xvrxvr/EventCalendar/spice/sch.asc

C1: cap; 47000µF; V=25 Irms=1
C2: cap; 1nF
D1: schottky; 30BQ060
L1: ind; 40mH; Rser=30
M1: pmos; AO6407
M2: pmos; IRF7406
M3: pmos; IRF7406
Q1: pnp; BC807-40
R1: res; 58
R2: res; 4.6
R3: res; 10K
R4: res; 3.6K
R5: res; 1.8K
R6: res; 5K
U1: TL431
V1: voltage; 15; Rser=0
V2: voltage; PULSE(0 -10 7 0.1 0.1 1000 100000 1)
V3: voltage; 12; Rser=0
Named nets: Vc, On, Sol, 0, R11, R12
.tran 0 15 0 startup uic
