xvrxvr/EventCalendar/soft/firmware/main/common.h

#pragma once

#include <assert.h>
#include <ctype.h>
#include <dirent.h>
#include <errno.h>
#include <inttypes.h>
#include <stdarg.h>
#include <stdint.h>
#include <stdio.h>
#include <stdlib.h>
#include <string.h>
#include <sys/types.h>
#include <time.h>

#include "estring.h"

#include <algorithm>
#include <atomic>
#include <limits>
#include <memory>
#include <optional>
#include <vector>
#include <utility>

// Converts to DOS encode. Returns encoded-size
// Zero terminated encoded buffer if 'length' is -1
int utf8_to_dos(char*, int length=-1);

#include "prnbuf.h"

#include <freertos/FreeRTOS.h>
#include <freertos/semphr.h>
#include <freertos/task.h>
#include <freertos/timers.h>

#include <esp_http_server.h>
#include <esp_log.h>
#include <esp_netif.h>
#include <esp_random.h>
#include <esp_spiffs.h>
#include <esp_system.h>
#include <esp_task_wdt.h>
#include <esp_wifi.h>
#include <mdns.h>
#include <nvs_flash.h>

#include "protocol_examples_utils.h"

#include <driver/gpio.h>
#include <driver/i2c.h>
#include <driver/ledc.h>
#include <driver/spi_master.h>
#include <driver/uart.h>

#include <lwip/apps/netbiosns.h>
#include <lwip/inet.h>

#include <esp_adc/adc_cali_scheme.h>
#include <esp_adc/adc_cali.h>
#include <esp_adc/adc_oneshot.h>

#include <soc/gpio_struct.h>
#include <soc/spi_struct.h>

#pragma GCC diagnostic push
#pragma GCC diagnostic ignored "-Wvolatile"
#include <hal/spi_ll.h>
#pragma GCC diagnostic pop

#define RES_Y 240	//Screen X axis resolution
#define RES_X 400	//Screen Y axis resolution

// Priorities of various tasks
enum TasksPriority {
    TP_Hardware = 5,    // Handling of HW input
    TP_WEBPing  = 1,    // WEB ping task
    TP_LogSender= 5     // Log senter task
};

// task stack sizes
enum TaskStackSize {
    TSS_WEBPing = 8192, // WEB Ping task
    TSS_LogSender = 2048 // Remote Log sender
};

// Generic consts
enum SetupConsts {
    SC_WEBPing_Pings = 2,   // Number of missing Pings to hit threshold
    SC_WEBPing_Time  = 500,  // Time (in MS) between WEB Pings
    SC_HW_INPUT_AUTO_OFF = 1000, // Time (in MS) to automatically passivating HW Input
    SC_TouchTrackInterval = 5, // Time between Touch Track samples (in ticks)
    SC_TouchTrackDeadZone = 5, // Minimal distance in Touch Track to report move
    SC_DebounceTime = 2,    // Debounce time (in ticks)
    SC_TurnoffDelay = 10*60,  // Delay before automatically turn off LCD (in seconds)
    SC_MaxFPScope = 99,     // Maximum FP match scope that not considered as duplication
    SC_FPScope100 = 100,    // What value of Scope equeal to 100% ?
    SC_MaxWS = 16,          // Maximum number of simulteniously opened Websockets
    SC_PingTimeout = 5,     // How much 'ping' signals can we wait for answer
    SC_FileBufSize = 1024,   // Size of buffers for internal file operations
    SC_MAX_CH = 6,          // Maximum number of Characters in FP template
    SC_MinMsgTime = 5000,   // Minimum time to display message (in ms)
    SC_ActivityQueueLength = 16,// Size of Activity Queue. It will holds all pending Actions when no active Activity exists.
    SC_FGEditAnimSpeed = 10, // Animation speed in ticks
    SC_AminPanelTitleGap = 8,// Gap between title line (in Animated panel) and body
    SC_KbMsgShow        = 3, // Time to show message in Keyboard manager (in seconds)
    SC_MultiSelectErr   = 1, // Time to show mesage 'Invalid - try egain" (in seconds)
    SC_LogTaskWKUP      = 100, // Log task forced waikup time (in ms)
    SC_ConnectTout      = 10,  // Timeout for reconnect attempt for Remote Logger (in seconds)
    SC_LogPort          = 5429, // Port of Log server
    SC_LogStartLim      = 1024, // Start memory limit for Remote Log system (to prevent hang on memory overflow on startup)
    SC_CoreFileChunk    = 4096, // Size of chunk of CoreFile when sending them over HTTP
};

#define FINGERPRINT_SENSOR_NORMAL_COLOR ALC_Breathing, ALC_Blue, 1
#define FINGERPRINT_SENSOR_HIDDEN       ALC_Off,       ALC_Red
#define FINGERPRINT_SENSOR_OOB_COLOR    ALC_Breathing, ALC_Red, 1

#define FGEDIT_ICON_COLOR_NOT_FILLED 0xC0,0xC0,0xC0
#define FGEDIT_ICON_COLOR_FILLING_SETUP {               \
    .type = AT_Triange,                                 \
    .color_from = rgb(FGEDIT_ICON_COLOR_NOT_FILLED),    \
    .color_to = 0,                                      \
    .length = 10                                        \
}

#define FGEDIT_ICON_COLOR_FILLED_SETUP {                \
    .type = AT_None,                                    \
    .color_from = 0                                     \
}

#define FGEDIT_ICON_COLOR_ERROR_SETUP {                 \
    .type = AT_Pulse,                                   \
    .color_from = rgb(FGEDIT_ICON_COLOR_NOT_FILLED),    \
    .color_to = rgb(0xFF, 0, 0),                        \
    .length = 20                                        \
}






void reboot(); // Delayed reboot
void send_web_ping_to_ws(const char* tag);

// Detect size of valie UTF8 encoded buffer and returns it. Detect last splitted UTF8 symbol and substruct it from 'length'
int valid_utf8_size(const char*, int length=-1);

struct U {
    char b[4];
};

U dos_to_utf8(char sym);

inline TickType_t s2ticks(uint32_t time) {return time * 1000 / portTICK_PERIOD_MS;}
inline TickType_t ms2ticks(uint32_t time) {return time && time < portTICK_PERIOD_MS ? 1 : time / portTICK_PERIOD_MS;}

// Convert timestamp to ticks
inline TickType_t hit_to_ticks(time_t tm) 
{
    return s2ticks(tm - time(NULL));
}

class Debouncer {
    uint8_t shift_reg = 0;
public:
    bool stable() const {return shift_reg == 0x55 || shift_reg == 0xAA;}    
    bool value() const {return shift_reg == 0x55;}
    void operator <<(bool sw) {shift_reg <<= 2; shift_reg |= sw ? 1 : 2;}
    void clear() {shift_reg = 0;}
};

inline constexpr uint32_t bit(int idx) {return 1 << idx;}

// In file open_doors.cpp
enum OpenDoorResult {
    ODR_Opened      = 0x0100,    // Door was opened. Door index in low 3 bits or FF if door index not known
    ODR_Finished    = 0x0200,    // User exit by 'X' icon
    ODR_Timeout     = 0x0400,    // Exit by timeout
    ODR_Login       = 0x0800,    // New user logged in. User ID in low 5 bit
    ODR_Touch       = 0x1000     // y in low byte, x in high 9 bits
};

// Run interactive GUI for Door open.
// 'door_index' is a door index to open
// Returns bitset of OpenDoorResult (and optionally new user ID in low 5 bits)
uint32_t open_door(int door_index);

// Do upper case (latin & DOS)
uint8_t upcase(uint8_t);

// Read file into 'dst', return true. If file not exists (or read error) - return false
bool read_file(Prn& dst, const char* fname);
