xvrxvr/EventCalendar/soft/firmware/main/hadrware.cpp

#include "common.h"
#include "hadrware.h"

#include "ILI9327_SHIELD.h"
#include "pins.h"
#include "activity.h"

static const char TAG[] = "HW";

#define MY_SPI_HOST    HSPI_HOST

static spi_device_handle_t lcd_spi, sol_spi;
static adc_oneshot_unit_handle_t adc1_handle;

static TaskHandle_t sol_task_handle;

R503 fp_sensor;
LCD lcd;

static const i2c_port_t i2c_master_port = I2C_NUM_0;

#define _RS_COMMAND  gpio_set_level(PIN_NUM_LCD_RS, 0)
#define _RS_DATA gpio_set_level(PIN_NUM_LCD_RS, 1)
#define _LCD_IDLE _RS_DATA

struct CS_EN {
    CS_EN() {gpio_set_level(PIN_NUM_LCD_CS, 0);}
    ~CS_EN() {gpio_set_level(PIN_NUM_LCD_CS, 1); _LCD_IDLE;}
};

struct LCDAccess {
    static int lock_count;
    LCDAccess() {if (!lock_count++) spi_device_acquire_bus(lcd_spi, portMAX_DELAY);}
    ~LCDAccess() {if (!--lock_count) spi_device_release_bus(lcd_spi);}
};

int LCDAccess::lock_count;

#define delay(v) vTaskDelay(ms2ticks(v))

static void sol_task(void*);

inline void LCD::write_lcd(uint8_t d)
{
    spi_transaction_t t{};

    t.length=8;
    t.tx_data[0]=d;
    t.flags = SPI_TRANS_USE_TXDATA;

    ESP_ERROR_CHECK(spi_device_polling_transmit(lcd_spi, &t));
}

#define LCD_HW SPI2

inline void wait4lcd_done() {while(!LCD_HW.slave.trans_done) {;}}
inline void wait4lcd_vacant() {wait4lcd_done(); while (LCD_HW.cmd.val) {;}}


inline void write_lcd_fast(uint8_t data)
{
    LCD_HW.slave.trans_done = 0;
    LCD_HW.data_buf[0] = data;
    LCD_HW.cmd.usr = 1;
    wait4lcd_done();

    GPIO.out_w1tc = 1 << PIN_NUM_LCD_WR;
    GPIO.out_w1ts = 1 << PIN_NUM_LCD_WR;
}

inline void LCD::_WRITE_DATA(uint8_t d)
{
    write_lcd(d);
    gpio_set_level(PIN_NUM_LCD_WR, 0);
    gpio_set_level(PIN_NUM_LCD_WR, 1);
}

inline void _WRITE_DATA_FAST(uint8_t d)
{
    write_lcd_fast(d);
}

inline void write_sol(uint8_t data)
{
    spi_transaction_t t{};

    t.length=8;
    t.tx_data[0]=data;
    t.flags = SPI_TRANS_USE_TXDATA;

    ESP_ERROR_CHECK(spi_device_polling_transmit(sol_spi, &t));
}


/* Internal function writes an 8 bit command byte to the display */
inline void LCD::_WriteCommand(uint8_t command)
{
	_RS_COMMAND;
	_WRITE_DATA(command);
}



/* Internal function writes an 8 bit data parameter byte to the display */
inline void _WriteData(uint8_t data)
{
	_RS_DATA;
	_WRITE_DATA_FAST(data);
}


/* Resets the interface */
void LCD::DReset(void)
{
	CS_EN cs_en;
	
	_WriteCommand(REG_RESET); //Soft reset
    delay(200);
}

// Writes the initial setting to the screen. Settings are taken from the ILI9325 application note.
void LCD::init_screen(void)
{
	DReset();	

    LCDAccess lcd_access;
    CS_EN cs_en;
	
	_WriteCommand(REG_DISPOFF);
	_WriteCommand(REG_EXITSLEEP);
	delay(120); //Must wait 120ms after exiting sleep 
	_WriteCommand(REG_CMDPROTECT);
	_WriteData(0x00);
	_WriteCommand(REG_DISPTIMING);
	_WriteData(0x10);
	_WriteData(0x10);
	_WriteData(0x02);
	_WriteData(0x02);
	_WriteCommand(REG_PANELDRIVE);
	_WriteData(0x00);
	_WriteData(0x35);
	_WriteData(0x00);
	_WriteData(0x00);
	_WriteData(0x01);
	_WriteData(0x02);
	_WriteCommand(REG_FRAMERATE);
	_WriteData(0x04);
	_WriteCommand(REG_PWRNORMMODE);
	_WriteData(0x01);
	_WriteData(0x04);
	_WriteCommand(REG_3GAMMA);
	_WriteData(0x80);
//	_WriteCommand(REG_ADDRMODE);
//	_WriteData(0x48);
	_WriteCommand(REG_PIXELFORMAT);
	_WriteData(0x55);
	_WriteCommand(REG_COLADDR);
	_WriteData(0x00);
	_WriteData(0x00);
	_WriteData(0x00);
	_WriteData(0xEF);
	_WriteCommand(REG_PAGEADDR);
	_WriteData(0x00);
	_WriteData(0x00);
	_WriteData(0x01);
	_WriteData(0x8F);
	_WriteCommand(REG_PARAREA);
	_WriteData(0x00);
	_WriteData(0x00);
	_WriteData(0x01);
	_WriteData(0x8F);
	_WriteCommand(REG_DISPON);
}

/* Places the screen in to or out of sleep mode where:
	mode is the required state. Valid values area
		true (screen will enter sleep state)
		false (screen will wake from sleep state)
*/
void LCD::DSleep(bool mode)
{
    {
        CS_EN cs_en;
    	
    	if(mode)
    	{
    		_WriteCommand(REG_ENTERSLEEP);
    	}
    	else
    	{
    		_WriteCommand(REG_EXITSLEEP);
    	}
    }
	delay(120);
} 
	



/* Turn the screen on or off where:
	mode is the required state. Valid values are
		ON (screen on)
		OFF (screen off)
*/
void LCD::DScreen(bool mode)
{
    CS_EN cs_en;
	
	if(mode)
		_WriteCommand(REG_DISPON);	//Screen on
	else
		_WriteCommand(REG_DISPOFF);  //Screen off
}




/* Sets the screen orientation and write direction where:
	mode is the direction, orientation to set the screen to. Valid vales are:
		SCREEN_NORMAL 		(Default)
		SCREEN_R90 			Screen is rotated 90o		
		SCREEN_R180 		Screen is rotated 180o
		SCREEN_R270 		Screen is rotated 270o		
*/
void LCD::DFlip(uint8_t mode)
{
	_FlipMode = mode;
	_res_x = RES_Y;
	_res_y = RES_X;
    CS_EN cs_en;
	switch(mode)
	{
		case(SCREEN_NORMAL): LCD_CtrlWrite_ILI9327(REG_ADDRMODE, 0b00001000); return;
		case(SCREEN_R90):	 LCD_CtrlWrite_ILI9327(REG_ADDRMODE, 0b10101000); break;
		case(SCREEN_R180):	 LCD_CtrlWrite_ILI9327(REG_ADDRMODE, 0b11001000); return;
		case(SCREEN_R270):	 LCD_CtrlWrite_ILI9327(REG_ADDRMODE, 0b00101000); break;	
	}
   	_res_x = RES_X;
   	_res_y = RES_Y;
}

/* Draws a solid rectangle to the using the current foreground colour where:
	x1 is the x coordinate of the top left corner of the rectangle.
	y1 is the y coordinate of the top left corner of the rectangle.
	x2 is the x coordinate of the bottom right corner of the rectangle.
	y2 is the y coordinate of the bottom right corner of the rectangle.
*/
void LCD::DRect(int16_t x1, int16_t y1, int16_t x2, int16_t y2, uint16_t color)
{
    LCDAccess lcd;
    CS_EN cs_en;
    
    _SetWriteArea(x1, y1, x2, y2);
    _WriteCommand(REG_WRITEMEM); //Write to RAM

    uint32_t total = (x2-x1+1)*(y2-y1+1);
    uint8_t col_high = color >> 8;
    uint8_t col_low = color & 0xFF;
    while(total--)
    {
        _WriteData(col_high); 
        _WriteData(col_low); 
    }
    wait4lcd_vacant();
}

// Draw buffer in format RGB888
void LCD::draw_rgb888(int16_t x1, int16_t y1, int16_t x2, int16_t y2, uint8_t* data)
{
    LCDAccess lcd;
    CS_EN cs_en;

    _SetWriteArea(x1, y1, x2, y2);
    _WriteCommand(REG_WRITEMEM); //Write to RAM

    for(int yy = y1; yy <= y2; ++yy)
    {
        for(int xx = x1; xx <= x2; ++xx, data += 3)
        {
            // |RRRRR:GGG|GGG:BBBBB|
            uint8_t color_high = (data[0] & 0xF8) | ((data[1] >> 5) & 7);
            uint8_t color_low = ((data[2] >> 3) & 0x1F) | ((data[1] << 3 ) & 0xE0);
            _WriteData(color_high); 
            _WriteData(color_low); 
        }
    }
    wait4lcd_vacant();
}

void LCD::WImgPallete(int16_t x1, int16_t y1, int16_t w, int16_t h, const uint8_t* image, const uint16_t* pallete, bool with_clip)
{
    if (with_clip) {WImgPalleteClip(x1, y1, w, h, image, pallete); return;}
    LCDAccess lcd;
    CS_EN cs_en;

    int16_t x2 = x1 + w - 1;
    int16_t y2 = y1 + h - 1;

    _SetWriteArea(x1, y1, x2, y2);
    _WriteCommand(REG_WRITEMEM); //Write to RAM
    for(int yy = y1; yy <= y2; ++yy)
    {
        for(int xx = x1; xx <= x2; ++xx, ++image)
        {
            uint16_t color = pallete[*image];
            _WriteData(uint8_t(color >> 8)); 
            _WriteData(uint8_t(color)); 
        }
    }
    wait4lcd_vacant();
}

void LCD::WImgPalleteClip(int16_t x1, int16_t y1, int16_t w, int16_t h, const uint8_t* image, const uint16_t* pallete)
{
    const uint8_t* row_end = image + w - 1;
    const uint8_t* start = image;
    int16_t start_row = 0;
    int16_t row = 0;

    auto flush = [&, this]()
    {
        if (row > start_row && start_row < h)
        {
            WImgPallete(x1, y1+start_row, w, row - start_row, start, pallete);
            start_row = row;
            start = image;
        }
    };

    for(; row < h; ++row, image += w, row_end += w)
    {
        if (*image == 0 || *row_end == 0)
        {
            flush();
            const uint8_t* b = image;
            const uint8_t* e = row_end+1;
            while(*b == 0 && b < e) ++b;
            while(e[-1] == 0 && b < e) --e;
            if (b != e) WImgPallete(x1 + (b-image), y1+row, e-b, 1, b, pallete);
            start = image + w;
            start_row = row+1;
        }
    }
    flush();
}

#define RNG(var, limit) if (var < 0) var = 0; else if (var >= limit) var = limit-1
void LCD::_SetWriteAreaDelta(int16_t& X1, int16_t& Y1, int16_t dx, int16_t dy)
{
    RNG(X1, _res_x);
    RNG(Y1, _res_y);
    int16_t X2 = X1 + dx - 1;
    int16_t Y2 = Y1 + dy - 1;
    _SetWriteArea(X1, Y1, X2, Y2);
}

void LCD::_SetWriteArea(int16_t& X1, int16_t& Y1, int16_t& X2, int16_t& Y2)
{
	//Make sure none of the area to write to is outside the display area. If so then crop it
    RNG(X1, _res_x);
    RNG(X2, _res_x);
    RNG(Y1, _res_y);
    RNG(Y2, _res_y);
#undef RNG
    if (X1 > X2) std::swap(X1, X2);
    if (Y1 > Y2) std::swap(Y1, Y2);

    uint16_t x1 = X1, x2 = X2, y1 = Y1, y2= Y2;

	//Adjust screen offset depending or orientation
	switch(_FlipMode)
	{
		case(SCREEN_NORMAL): break;
		case(SCREEN_R270): std::swap(x1, y1); std::swap(x2, y2); break;
			
		case(SCREEN_R90): std::swap(x1, y1); std::swap(x2, y2); break;
//			y1 += 32;
//			y2 += 32;
			break;
			
		case(SCREEN_R180):
//			x1 += 32;
//			x2 += 32;
			break;
	}
    LCDAccess lcd_access;
	
	//Set the memory write window
	_WriteCommand(REG_COLADDR);
	_WriteData(y1>>8);
	_WriteData(y1);
	_WriteData(y2>>8);
	_WriteData(y2);
	_WriteCommand(REG_PAGEADDR);
	_WriteData(x1>>8);
	_WriteData(x1);
	_WriteData(x2>>8);
	_WriteData(x2);
}



/* Internal function that writes 16 bits of data to one of the displays registers */
void LCD::LCD_CtrlWrite_ILI9327(uint8_t command, uint8_t data)
{
    LCDAccess lcd_access;
	_WriteCommand(command);
	_WriteData(data);
}

static const uint8_t font[] = {
    0x00,0x00,0x00,0x00,0x00,0x00,0x00,0x00,0x00,0x00,0x00,0x00,0x00,0x00,0x00,0x00,

// Symbol BS:   1, 2    (Len 2 - 1,2)
    0x00, 0x00, 0x07, 0x0F, 0x18, 0x33, 0x61, 0xC0, 0x61, 0x33, 0x18, 0x0F, 0x07, 0x00, 0x00, 0x00,
    0x00, 0x00, 0xFE, 0xFE, 0x06, 0x36, 0xE6, 0xC6, 0xE6, 0x36, 0x06, 0xFE, 0xFE, 0x00, 0x00, 0x00,
// Symbol ENT:  3, 4, 5 (Len 2 - 3, 4; Len 3 - 3,5,4)
    0x00, 0x00, 0x00, 0x0C, 0x18, 0x30, 0x60, 0xFF, 0xFF, 0x60, 0x30, 0x18, 0x0C, 0x00, 0x00, 0x00,
    0x00, 0x00, 0x00, 0x00, 0x00, 0x06, 0x06, 0xFE, 0xFE, 0x00, 0x00, 0x00, 0x00, 0x00, 0x00, 0x00,
    0x00, 0x00, 0x00, 0x00, 0x00, 0x00, 0x00, 0xFF, 0xFF, 0x00, 0x00, 0x00, 0x00, 0x00, 0x00, 0x00,
// Symbol SP:   6, 7, 8  (Len 2: 6,7, Len 3... - 6, 8..., 7)
    0x00, 0x00, 0x00, 0x00, 0x00, 0x00, 0x00, 0x00, 0x60, 0x60, 0x7F, 0x7F, 0x00, 0x00, 0x00, 0x00,
    0x00, 0x00, 0x00, 0x00, 0x00, 0x00, 0x00, 0x00, 0x06, 0x06, 0xFE, 0xFE, 0x00, 0x00, 0x00, 0x00,
    0x00, 0x00, 0x00, 0x00, 0x00, 0x00, 0x00, 0x00, 0x00, 0x00, 0xFF, 0xFF, 0x00, 0x00, 0x00, 0x00,
// Symbol Lang:  9
    0x00, 0x00, 0x00, 0x3C, 0x5A, 0xA5, 0xFF, 0xA5, 0xFF, 0xA5, 0x5A, 0x3C, 0x00, 0x00, 0x00, 0x00,

//    0x00,0x00,0x7e,0x81,0xa5,0x81,0x81,0xbd,0x99,0x81,0x81,0x7e,0x00,0x00,0x00,0x00,
//    0x00,0x00,0x7e,0xff,0xdb,0xff,0xff,0xc3,0xe7,0xff,0xff,0x7e,0x00,0x00,0x00,0x00,
//    0x00,0x00,0x00,0x00,0x6c,0xfe,0xfe,0xfe,0xfe,0x7c,0x38,0x10,0x00,0x00,0x00,0x00,
//    0x00,0x00,0x00,0x00,0x10,0x38,0x7c,0xfe,0x7c,0x38,0x10,0x00,0x00,0x00,0x00,0x00,
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
{
    LCDAccess lcd;
    CS_EN cs_en;

    const uint8_t fc_high = uint8_t(color >> 8);
    const uint8_t fc_low = uint8_t(color);
    
    _SetWriteAreaDelta(x, y, 32, 32);
    _WriteCommand(REG_WRITEMEM); //Write to RAM

    for(int dy=0; dy<32; ++dy, ++y)
    {
        uint32_t bits = *icon++;
        uint8_t cnt=32;
        do {
            if (bits&0x80000000) {_WriteData(fc_high); _WriteData(fc_low);}
            else {_WriteData(bc_high); _WriteData(bc_low);}
            bits <<= 1;
        } while (--cnt);
    }
    wait4lcd_vacant();
}

void LCD::text2(const char* text, int16_t x, int16_t y, int txt_len)
{
    LCDAccess lcd;
    CS_EN cs_en;

    if (txt_len == -1) txt_len = strlen(text);
    if (x == -1) x = midx(txt_len*2);
    _SetWriteAreaDelta(x, y, txt_len<<4, 32);
    _WriteCommand(REG_WRITEMEM); //Write to RAM

    for(uint8_t scan_line=0; scan_line!=32; ++scan_line)
    {
        int tl = txt_len;
        for(const char* t=text;tl--; ++t)
        {
            uint8_t sym = *t;
            uint8_t bits = font[sym*16+(scan_line>>1)];
            uint8_t cnt=8;
            do {
                if (bits&0x80) {_WriteData(fc_high); _WriteData(fc_low); _WriteData(fc_high); _WriteData(fc_low);}
                else {_WriteData(bc_high); _WriteData(bc_low); _WriteData(bc_high); _WriteData(bc_low);}
                bits <<= 1;
            } while (--cnt);
        }
    }
    wait4lcd_vacant();
}

#undef _B
#define _B(n) (1ull<<(n))

void hw_init()
{
    gpio_set_level(PIN_NUM_OE_SOL, 1);
    gpio_set_level(PIN_NUM_LCD_CS, 1);
    gpio_set_level(PIN_NUM_LCD_SW1, 1);
    gpio_set_level(PIN_NUM_LCD_SW2, 1);
    gpio_set_level(PIN_NUM_LCD_WR, 1);
    gpio_set_level(PIN_NUM_LCD_BL, 1);

    gpio_config_t gpio_cfg_out = {
        .pin_bit_mask = _B(PIN_NUM_OE_SOL)|_B(PIN_NUM_LCD_CS)|_B(PIN_NUM_LCD_BL)|_B(PIN_NUM_LCD_SW1)|_B(PIN_NUM_LCD_SW2)|_B(PIN_NUM_LCD_WR)|_B(PIN_NUM_LCD_RS),
        .mode = GPIO_MODE_OUTPUT,
        .pull_up_en = GPIO_PULLUP_DISABLE,
        .pull_down_en = GPIO_PULLDOWN_DISABLE,
        .intr_type = GPIO_INTR_DISABLE
    };
    ESP_ERROR_CHECK(gpio_config(&gpio_cfg_out));
    gpio_config_t gpio_cfg_in = {
        .pin_bit_mask = _B(PIN_NUM_FP_WAKEUP)|_B(PIN_NUM_DIPSW_BOOT)|_B(PIN_NUM_DIPSW_AUX),
        .mode = GPIO_MODE_INPUT,
        .pull_up_en = GPIO_PULLUP_ENABLE,
        .pull_down_en = GPIO_PULLDOWN_DISABLE,
        .intr_type = GPIO_INTR_DISABLE
    };
    ESP_ERROR_CHECK(gpio_config(&gpio_cfg_in));

    gpio_set_level(PIN_NUM_OE_SOL, 1);
    gpio_set_level(PIN_NUM_LCD_CS, 1);
    gpio_set_level(PIN_NUM_LCD_SW1, 1);
    gpio_set_level(PIN_NUM_LCD_SW2, 1);
    gpio_set_level(PIN_NUM_LCD_WR, 1);
    gpio_set_level(PIN_NUM_LCD_BL, 1);

    gpio_set_intr_type(PIN_NUM_FP_WAKEUP, GPIO_INTR_NEGEDGE);
    gpio_set_intr_type(PIN_NUM_LCD_RS, GPIO_INTR_ANYEDGE); // This is Touch sence pin

    spi_bus_config_t buscfg={
        .mosi_io_num=PIN_NUM_MOSI,
        .miso_io_num=-1,
        .sclk_io_num=PIN_NUM_CLK,
        .quadwp_io_num=-1,
        .quadhd_io_num=-1,
        .max_transfer_sz=10
    };
    spi_device_interface_config_t lcd_devcfg={
        .mode=0,
        .clock_speed_hz=SPI_MASTER_FREQ_80M,
        .spics_io_num=PIN_NUM_CS_LCD,
        .flags = SPI_DEVICE_NO_DUMMY,
        .queue_size=1
    };
    spi_device_interface_config_t sol_devcfg={
        .mode=0,
        .clock_speed_hz=SPI_MASTER_FREQ_10M,
        .spics_io_num=PIN_NUM_CS_SOL,
        .queue_size=1
    };
    //Initialize the SPI bus
    ESP_ERROR_CHECK(spi_bus_initialize(MY_SPI_HOST, &buscfg, SPI_DMA_CH_AUTO));

    //Attach the LCD to the SPI bus
    ESP_ERROR_CHECK(spi_bus_add_device(MY_SPI_HOST, &lcd_devcfg, &lcd_spi));

    //Attach the Solenoids to the SPI bus
    ESP_ERROR_CHECK(spi_bus_add_device(MY_SPI_HOST, &sol_devcfg, &sol_spi));

    // Zero Solenoid register, then OE it
    write_sol(0);
    gpio_set_level(PIN_NUM_OE_SOL, 0);

    // ADC config
    adc_oneshot_unit_init_cfg_t init_config1 = {
        .unit_id = ADC_UNIT_1,
    };
    ESP_ERROR_CHECK(adc_oneshot_new_unit(&init_config1, &adc1_handle));

    adc_oneshot_chan_cfg_t config = {
        .atten = ADC_ATTEN_DB_11,
        .bitwidth = ADC_BITWIDTH_DEFAULT,
    };
    ESP_ERROR_CHECK(adc_oneshot_config_channel(adc1_handle, ADC_Y_PLUS, &config));
    ESP_ERROR_CHECK(adc_oneshot_config_channel(adc1_handle, ADC_X_MINUS, &config));

    // LCD
    delay(50);
    {
	    lcd.init_screen();
    	lcd.DFlip(LCD::SCREEN_MY);
    	lcd.DRect(0, 0, LCD::MAX, LCD::MAX, 0);
    }

    // Configure I2C
    i2c_port_t i2c_master_port = I2C_NUM_0;
    i2c_config_t conf = {
        .mode = I2C_MODE_MASTER,
        .sda_io_num = PIN_NUM_I2C_SDA,
        .scl_io_num = PIN_NUM_I2C_SCL,
        .sda_pullup_en = GPIO_PULLUP_DISABLE,
        .scl_pullup_en = GPIO_PULLUP_DISABLE,
        .master = {
            .clk_speed = 100'000
        }
    };

    i2c_param_config(i2c_master_port, &conf);

    ESP_ERROR_CHECK(i2c_driver_install(i2c_master_port, conf.mode, 0, 0, 0));

    ESP_ERROR_CHECK(ledc_fade_func_install(ESP_INTR_FLAG_LEVEL1));

    ledc_timer_config_t ledc_timer = {
        .speed_mode       = LEDC_HIGH_SPEED_MODE,
        .duty_resolution  = LEDC_TIMER_13_BIT,
        .timer_num        = LEDC_TIMER_0,
        .freq_hz          = 5000,  // Set output frequency at 5 kHz
        .clk_cfg          = LEDC_AUTO_CLK
    };
    ESP_ERROR_CHECK(ledc_timer_config(&ledc_timer));

    // Prepare and then apply the LEDC PWM channel configuration
    ledc_channel_config_t ledc_channel = {
        .gpio_num       = PIN_NUM_LCD_BL,
        .speed_mode     = LEDC_HIGH_SPEED_MODE,
        .channel        = LEDC_CHANNEL_0,
        .intr_type      = LEDC_INTR_DISABLE,
        .timer_sel      = LEDC_TIMER_0,
        .duty           = (1<<13)-1,
        .hpoint         = 0
    };
    ESP_ERROR_CHECK(ledc_channel_config(&ledc_channel));

    const uart_port_t uart_num = UART_NUM_2;
    uart_config_t uart_config = {
        .baud_rate = 57600,
        .data_bits = UART_DATA_8_BITS,
        .parity = UART_PARITY_DISABLE,
        .stop_bits = UART_STOP_BITS_1,
        .flow_ctrl = UART_HW_FLOWCTRL_DISABLE,
        .rx_flow_ctrl_thresh = 0,
        .source_clk = UART_SCLK_DEFAULT
    };
    // Configure UART parameters
    ESP_ERROR_CHECK(uart_param_config(uart_num, &uart_config));
    ESP_ERROR_CHECK(uart_set_pin(UART_NUM_2, PIN_NUM_FP_RXD, PIN_NUM_FP_TXD, -1, -1));

    ESP_ERROR_CHECK(uart_driver_install(UART_NUM_2, 2048, 0, 0, NULL, 0));

    xTaskCreate(sol_task, "Sol", 2048, NULL, tskIDLE_PRIORITY+1, &sol_task_handle);

    delay(150);
    auto err = fp_sensor.init();
    
    if (err != R503_SUCCESS)
    {
        printf("FP_sensor init error: %s\n", R503::errorMsg(err));
        abort();
    }
    fp_sensor.setAuraLED(auraOff);
}
#undef _B


void sol_hit(int index)
{
    xTaskNotify(sol_task_handle, (index&7)+1, eSetValueWithOverwrite);
    ESP_LOGI(TAG, "Sol: Signal %d", index);
}

/*
    BL      - 5           LCD    TouchX TouchXInv TouchY  TouchYInv  TouchSence     TouchSence/Alt    Idle
    DB7/Y- (SW1) - 27    1/DB7     0      0         1/0     1/1          1/0             0             1/1
    DB6/X+ (SW2) - 26    1/DB6    1/1    1/0         0       0            0             1/0            1/1
    WR/Y+   - 21          WR      ADC    ADC         1       0            0           PullUP/Sence      1       -> 36 (SENSOR_VP)
    RS/X-   - 19          RS       0      1         ADC     ADC        PullUP/Sence      0              1       -> 39 (SENSOR_VN)
*/

enum TTSetup {
    TTS_SW1     = 0x01,
    TTS_SW2     = 0x02,
    TTS_WR_ADC  = 0x04,
    TTS_WR      = 0x08,
    TTS_RS_ADC  = 0x10,
    TTS_RS      = 0x20,
    TTS_DB6     = 0x40,   // Do not change value!
    TTS_DB7     = 0x80,   // Do not change value!
    TTS_RS_SNS  = 0x100
};

static const int tts_setup [] = {
    TTS_SW1 | TTS_SW2 | TTS_WR | TTS_RS,         // TT_LCD
    TTS_SW2 | TTS_DB6 | TTS_WR_ADC,              // TT_X
    TTS_SW2 | TTS_WR_ADC | TTS_RS,               // TT_XInv
    TTS_SW1 | TTS_WR | TTS_RS_ADC,               // TT_Y
    TTS_SW1 | TTS_DB7 | TTS_RS_ADC,              // TT_YInv
    TTS_SW1 | TTS_RS_SNS                         // TT_Sence
};

#define NOP() __asm volatile("nop")

static const int adc_reads = 255;

int touch_config(TouchType tt)
{
    int read_adc = -1;
    int setup = tts_setup[tt];
#define V(name) ((setup & TTS_##name) != 0)
    wait4lcd_vacant();
    lcd.write_lcd(setup & 0xC0); // DB6 & DB7
    gpio_set_level(PIN_NUM_LCD_SW1, V(SW1));
    gpio_set_level(PIN_NUM_LCD_SW2, V(SW2));

    if (setup & TTS_WR_ADC) {gpio_set_direction(PIN_NUM_LCD_WR, GPIO_MODE_DISABLE); read_adc = ADC_Y_PLUS;}
    else {gpio_set_level(PIN_NUM_LCD_WR, V(WR)); gpio_set_direction(PIN_NUM_LCD_WR, GPIO_MODE_OUTPUT);}

    if (setup & TTS_RS_SNS) 
    {
        // Precharge
        gpio_set_direction(PIN_NUM_LCD_RS, GPIO_MODE_OUTPUT);
        gpio_set_level(PIN_NUM_LCD_RS, 1);
        NOP(); NOP();
        // Sence
        gpio_set_direction(PIN_NUM_LCD_RS, GPIO_MODE_INPUT); 
        gpio_set_pull_mode(PIN_NUM_LCD_RS, GPIO_PULLUP_ONLY); 
        NOP(); NOP(); 
        return gpio_get_level(PIN_NUM_LCD_RS);
    } else
    if (setup & TTS_RS_ADC) {gpio_set_pull_mode(PIN_NUM_LCD_RS, GPIO_FLOATING); gpio_set_direction(PIN_NUM_LCD_RS, GPIO_MODE_DISABLE); read_adc = ADC_X_MINUS;} 
    else {gpio_set_level(PIN_NUM_LCD_RS, V(RS)); gpio_set_direction(PIN_NUM_LCD_RS, GPIO_MODE_OUTPUT);}
#undef V

    if (read_adc != -1)
    {
        int result = 0;
        vTaskDelay(1);

        for(int i=0; i<adc_reads; ++i)
        {
            int value = 0;
            ESP_ERROR_CHECK(adc_oneshot_read(adc1_handle, (adc_channel_t)read_adc, &value));
            result += value;
        }
        return result / adc_reads;
    }

    return 0;
}

TouchConfig::TouchConfig() {x=y=-1; touched();}
TouchConfig::~TouchConfig() {touch_config(TT_LCD);}

bool TouchConfig::raw_touch_read(int& x, int& y)
{
    x = touch_config(TT_X);
//  y = touch_config(TT_Y);
//  if (y < min_y) y = mid_y - touch_config(TT_YInv);
    y = touch_config(TT_YInv); // Inverted part has higher minimum value (about threshold - 240-250). Not-inverted has minimum of 78
    return !touch_config(TT_Sence);
}

int TouchConfig::raw_touch_config(TouchType tt) {return touch_config(tt);}

constexpr int32_t mid_y = 2850;
constexpr int32_t min_y = 300;

bool TouchConfig::touched()
{
    x=y=-1;
    Debouncer db;
    for(int i=0; i<100; ++i)
    {
        db << !touch_config(TT_Sence);
        if (db.stable())
        {
            if (!db.value()) return false;
            if (raw_touch_read()) return true;
            db.clear();
        }
    }
    printf("TouchConfig: Can't get Touch status for 100 samples!\n");
    return false;
}

void TouchConfig::wait_press()
{
    while(!touched())
    {
        touch_config(TT_LCD);
        delay(10);
    }
}

void TouchConfig::wait_release()
{
    while(touched())
    {
        touch_config(TT_LCD);
        delay(10);
    }
}

volatile uint8_t time_to_reengage_sol = 10;

static void reengage_sol()
{
    uint8_t cnt = 10;
    time_to_reengage_sol = cnt;
    do {delay(1000); time_to_reengage_sol = --cnt;} while(cnt);
}

static void sol_task(void*)
{
    reengage_sol();
    for(;;)
    {
        uint32_t index = ulTaskNotifyTake(pdTRUE, portMAX_DELAY); 
        ESP_LOGI(TAG, "Sol: execute %lu", index-1);
        if (index > 0 && index <= 8)
        {
            --index;
            static const uint8_t enc[] = {5, 4, 6, 7, 3, 8, 1, 2};
            write_sol(bit(enc[index]-1));
            time_to_reengage_sol = 15;
            delay(5000);
            write_sol(0);
            reengage_sol();
        }
    }
}


#define I2C_MASTER_TIMEOUT   (1000/portTICK_PERIOD_MS)

int get_temperature()
{
    // Temperature
    int8_t data[2] = {0};
    ESP_ERROR_CHECK(i2c_master_read_from_device(i2c_master_port, 0x48, (uint8_t *)data, 2, I2C_MASTER_TIMEOUT));
    return data[0];
}


static uint8_t bcd2bin(uint8_t bcd)
{
    return (bcd >> 4) * 10 + (bcd & 0xF);
}

static uint8_t bin2bcd(uint8_t bin)
{
    return ((bin / 10) << 4) | (bin % 10);
}

bool RTC::read()
{
     uint8_t ptr=0;
     uint8_t data[8];

     ESP_ERROR_CHECK(i2c_master_write_read_device(i2c_master_port, 0xD0>>1, &ptr, 1, data, 8, I2C_MASTER_TIMEOUT));

     seconds = bcd2bin(data[0] & 0x7F);
     minutes = bcd2bin(data[1] & 0x7F);
     hours = bcd2bin(data[2] & 0x3F);
     day = data[3] & 7;
     date = bcd2bin(data[4] & 0x3F);
     month = bcd2bin(data[5] & 0x1F);
     year = bcd2bin(data[6]);

     return (data[0] & 0x80) == 0;
}

void RTC::write()
{
    uint8_t data[9];

    data[0] = 0;
    data[1] = bin2bcd( seconds) & 0x7F;
    data[2] = bin2bcd( minutes) & 0x7F;
    data[3] = (bin2bcd( hours  ) & 0x3F) | 0x40;
    data[4] = day & 7;
    data[5] = bin2bcd( date   ) & 0x3F;
    data[6] = bin2bcd( month  ) & 0x1F;
    data[7] = bin2bcd( year  );
    data[8] = 0;

    ESP_ERROR_CHECK(i2c_master_write_to_device(i2c_master_port, 0xD0>>1, data, 9, I2C_MASTER_TIMEOUT));
}

void RTC::start()
{
    uint8_t data[2];

    data[0] = 0;
    data[1] = 0;
    ESP_ERROR_CHECK(i2c_master_write_to_device(i2c_master_port, 0xD0>>1, data, 2, I2C_MASTER_TIMEOUT));
}

void RTC::read_ram(void* dst, uint8_t shift, uint8_t size)
{
     uint8_t ptr = 8 + shift;

     ESP_ERROR_CHECK(i2c_master_write_read_device(i2c_master_port, 0xD0>>1, &ptr, 1, (uint8_t*)dst, size, I2C_MASTER_TIMEOUT));
}

void RTC::write_ram(const void* src, uint8_t shift, uint8_t size)
{
    uint8_t buf[57];
    assert(size <= 56);

    buf[0] = 8 + shift;
    memcpy(buf+1, src, size);
    ESP_ERROR_CHECK(i2c_master_write_to_device(i2c_master_port, 0xD0>>1, buf, size+1, I2C_MASTER_TIMEOUT));
}

#define I2C_TRANS_BUF_MINIMUM_SIZE 128

static esp_err_t i2c_master_probe_to_device(i2c_port_t i2c_num, uint8_t device_address, TickType_t ticks_to_wait)
{
    esp_err_t err = ESP_OK;
    uint8_t buffer[I2C_TRANS_BUF_MINIMUM_SIZE] = { 0 };

    i2c_cmd_handle_t handle = i2c_cmd_link_create_static(buffer, sizeof(buffer));
    assert (handle != NULL);

    err = i2c_master_start(handle);
    if (err != ESP_OK) {
        goto end;
    }

    err = i2c_master_write_byte(handle, device_address << 1 | I2C_MASTER_WRITE, true);
    if (err != ESP_OK) {
        goto end;
    }

    i2c_master_stop(handle);
    err = i2c_master_cmd_begin(i2c_num, handle, ticks_to_wait);

end:
    i2c_cmd_link_delete_static(handle);
    return err;
}

static esp_err_t i2c_master_write2_to_device(i2c_port_t i2c_num, uint8_t device_address,
                                     const uint8_t* write_buffer, size_t write_size,
                                     const uint8_t* write_buffer2, size_t write_size2,
                                     TickType_t ticks_to_wait)
{
    esp_err_t err = ESP_OK;
    uint8_t buffer[I2C_TRANS_BUF_MINIMUM_SIZE] = { 0 };

    i2c_cmd_handle_t handle = i2c_cmd_link_create_static(buffer, sizeof(buffer));
    assert (handle != NULL);

    err = i2c_master_start(handle);
    if (err != ESP_OK) {
        goto end;
    }

    err = i2c_master_write_byte(handle, device_address << 1 | I2C_MASTER_WRITE, true);
    if (err != ESP_OK) {
        goto end;
    }

    err = i2c_master_write(handle, write_buffer, write_size, true);
    if (err != ESP_OK) {
        goto end;
    }

    err = i2c_master_write(handle, write_buffer2, write_size2, true);
    if (err != ESP_OK) {
        goto end;
    }

    i2c_master_stop(handle);
    err = i2c_master_cmd_begin(i2c_num, handle, ticks_to_wait);

end:
    i2c_cmd_link_delete_static(handle);
    return err;
}


// Page writes performed on page boundaries - page write will wrap around if address+size will cross 32 byte block
void EEPROM::write(uint16_t address, const void* data, uint8_t size)
{
    assert(size <= 32);
    poll4ready();
    uint8_t addr[2] = {uint8_t(address >> 8), uint8_t(address)}; 
    esp_err_t err;
    for(int i=0; i<10; ++i)
    {
        err = i2c_master_write2_to_device(i2c_master_port, 0xA0>>1, addr, 2,  (const uint8_t*)data, size, I2C_MASTER_TIMEOUT);
        if (ESP_OK == err) return;
    }
    ESP_ERROR_CHECK(err);
}

void EEPROM::read(uint16_t address, void* data, uint8_t size)
{
    poll4ready();
    uint8_t addr[2] = {uint8_t(address >> 8), uint8_t(address)};
    esp_err_t err;
    for(int i=0; i<10; ++i)
    {
        err = i2c_master_write_read_device(i2c_master_port, 0xA0>>1, addr, 2, (uint8_t*)data, size, I2C_MASTER_TIMEOUT);
        if (ESP_OK == err) return;
    }
    ESP_ERROR_CHECK(err);
}

void EEPROM::poll4ready()
{
    while(i2c_master_probe_to_device(i2c_master_port, 0xA0>>1, I2C_MASTER_TIMEOUT)) {;}
}

void fade_out()
{
    ESP_ERROR_CHECK(ledc_set_fade_time_and_start(LEDC_HIGH_SPEED_MODE, LEDC_CHANNEL_0, 0, 1000, LEDC_FADE_WAIT_DONE));
}

void fade_in()
{
    ESP_ERROR_CHECK(ledc_set_fade_time_and_start(LEDC_HIGH_SPEED_MODE, LEDC_CHANNEL_0, (1<<LEDC_TIMER_13_BIT)-1, 1000, LEDC_FADE_WAIT_DONE));
}

bool test_wakeup() {return !gpio_get_level(PIN_NUM_FP_WAKEUP);}

#if 0
static esp_err_t destroy_my_pannel(esp_lcd_panel_handle_t h) {delete h; return ESP_OK;}

static esp_err_t mirror_my_pannel(esp_lcd_panel_t *panel, bool x_axis, bool y_axis)
{
    return ESP_OK;
}

static esp_err_t swap_my_pannel(esp_lcd_panel_t *panel, bool swap_axes)
{
    return ESP_OK;
}

static esp_err_t set_gap_my_pannel(esp_lcd_panel_t *panel, int x_gap, int y_gap)
{
    return ESP_OK;
}

static esp_err_t invert_color_my_pannel(esp_lcd_panel_t *panel, bool invert_color_data)
{
    return ESP_OK;
}

esp_err_t draw_my_pannel(esp_lcd_panel_t *, int x1, int y1, int x2, int y2, const void *color_data)
{
    LCDAccess lcd;

	if(x1 < _res_x && x2 >= 0 && y1 < _res_y && y2 >= 0) 
	{
        CS_EN cs_en;
		
		if(x1 < 0)	x1 = 0;
		if(y1 < 0)	y1 = 0;
		if(x2 > _res_x) x2 = _res_x ;
		if(y2 > _res_y) y2 = _res_y;

        --x2; --y2;
	
		_SetWriteArea(x1, y1, x2, y2);
		_WriteCommand(REG_WRITEMEM); //Write to RAM
	
		uint32_t total = (x2-x1+1)*(y2-y1+1);
        const uint8_t* c = (const uint8_t*)color_data; // <R><G><B> ?
#define R c[0]
#define G c[1]
#define B c[2]        
        while(total--)
   		{
   			_WriteData( ((G & 0x1C) << 3) | (B >> 3) ); 
   			_WriteData( (R & 0xF8) | ((G & 0xE0) >> 5) );
            c += 3;
   		}
#undef R
#undef G
#undef B
	}
    return ESP_OK;
}

esp_lcd_panel_handle_t esp_lcd_new_panel_my()
{
    return new esp_lcd_panel_t{
        .reset = DReset,
        .init = init_screen,
        .del = destroy_my_pannel,
        .draw_bitmap = draw_my_pannel,
        .mirror = mirror_my_pannel,
        .swap_xy = swap_my_pannel,
        .set_gap = set_gap_my_pannel,
        .invert_color = invert_color_my_pannel,
        .disp_on_off = DScreen
    };
}
#endif

LCD& Activity::LCDAccess::access() {return lcd;}
R503& Activity::FPAccess::access() {return fp_sensor;}

bool override_switch_active()
{
    return !gpio_get_level(PIN_NUM_DIPSW_AUX);
}
