xvrxvr/EventCalendar/soft/firmware/main/grid_mgr.h

#pragma once

#include "text_draw.h"

namespace GridManager {


enum UpdateItem {
    UI_Text  = 0x01,
    UI_Box   = 0x02
};

struct MiniCell {
    int id=-1;
    int col_span=1;
};

struct Row {
    std::vector<MiniCell> cells;
    int total=0;

    void add_string(const char*);
public:
    Row(const char* s = NULL) {if (s) add_string(s);}

    Row& operator () (const char* s) {add_string(s); return *this;}
    Row& operator () (int id, int col_span=1) {assert(col_span>=1); cells.push_back(MiniCell{id, col_span}); total+=col_span; return *this;}

    size_t row_size() const {return total;}

    MiniCell operator() (int col) const {return col < cells.size() ? cells[col] : MiniCell{};}
};

class Rows {
    std::vector<Row> rows;
public:
    Rows& operator << (const Row& r) {rows.push_back(r); return *this;}

    size_t row_size() const 
    {
        size_t result = 0;
        for(const auto& r: rows) result = std::max(result, r.row_size());
        return result;
    }
    size_t total_rows() const {return rows.size();}

    MiniCell operator() (int row, int col) const {return rows[row](col);}
};

class Geometry {
    Rows rows;
public:
    Geometry(const Rows& r) : rows(r) {}

    size_t row_size() const  {return rows.row_size();}
    size_t total_rows() const {return rows.total_rows();}
    MiniCell cell(int row, int col) const {return rows(row, col);}
};

struct Rect {
    int x=-1;
    int y=-1;
    int width=0;
    int height=0;
};

constexpr int TotalBoxDefs = 5;
struct BoxDef {
    const char* box_defs[TotalBoxDefs] = {};
    int16_t reserve_top = 0; // -1 for reserve all availabe space
    int16_t reserve_left = 0; // -1 for reserve all availabe space
    int16_t cell_width = 0; // Set to >0 value to define internal cell width. By default defined by cell contents
    int16_t cell_height = 16; // Define internal cell height.
};

class Grid {
    struct Cell : public MiniCell {
        Rect box;      // x,y from top/left of internal Grid area (grid_bounds). box itself represents Box for this cell (not internal contents)
        int updated=0; // bitset of UpdateItem
        int box_index = 1;
    };
    BoxDef bdef;
    const Geometry* geom;
    int strip_lines = 0;

    int col_count=0;
    int row_count=0;
    std::vector<Cell> cells;

    Rect bounds; // External box coordinates. Set by 'set_coord' method call
    Rect grid_bounds; // Rect of grid itself. width & haight depends on grid only, but x & y will be set by 'set_coord' method call

    int16_t prev_dx = 0;  // Previous dx/dy in 'draw_float' call
    int16_t prev_dy = 0;

    Cell& cell(int row, int col) {return cells[col + row*col_count];}

    const Cell& cell(int row, int col) const {return cells[col + row*col_count];}

    static Rect shrink(const Rect& out_box, const TextBoxDraw::TextGlobalDefinition&);

    // Performs initial Geometry evaluation.
    // Called at beginig of EVERY interface function, but really executed only once
    void initial_geom_eval();

    // Draw one cell
    void draw_cell(LCD& lcd, const Cell& cell, int update, int dx, int dy);

    // Draw spacer
    void draw_spacer(LCD& lcd, const Rect&);

    // Draw spacer between boxes
    void draw_spacer(LCD& lcd, const Rect& b1, const Rect& b2, int dx, int dy);

    // Draw diff spacer for floating rect
    void draw_float_spacer(LCD& lcd, int row, int col, int row_count, int col_count, int dx, int dy);
protected:
    TextBoxDraw::TextGlobalDefinition box_defs[TotalBoxDefs];

public:
    Grid(const BoxDef& b, const Geometry& g, int strip_lines=0) : bdef(b), geom(&g), strip_lines(strip_lines) 
    {
        for(int i=0; i<TotalBoxDefs; ++i)
        {
            if (auto str = b.box_defs[i]) box_defs[i].setup(str);
        }
    }

    // Callback for cell text. Returns NULL if no text required
    virtual const char* get_text_dos(const MiniCell&) = 0;

    ///////////// Run time coordinates info //////////////////////////

    // Returns coordinates of outer box
    Rect get_coord() {initial_geom_eval(); return bounds;}

    // Return rectangle of cell outer part
    Rect get_cell_coord_ext(int row, int col) const {return cell(row, col).box;}

    // Return rectangle of cell internals (greed coordinates)
    Rect get_cell_coord_int(int row, int col) const 
    {
        const auto& c = cell(row, col) ;
        return shrink(c.box, box_defs[c.box_index]);
    }

    Rect greed2screen(const Rect& rect)
    {
        Rect result(rect);
        result.x += grid_bounds.x;
        result.y += grid_bounds.y;
        return result;
    }

    // Return reserved space Rect
    Rect get_reserved(bool top_part=true)
    {
        initial_geom_eval();
        Rect inner = shrink(bounds, box_defs[0]);
        if (top_part) inner.height = bdef.reserve_top; else
        {
            inner.width = bdef.reserve_left;
            if (bdef.reserve_top) // Top also reserved - shrink pane by shifting start down
            {
                int cut = bdef.reserve_top + 2 * box_defs[0].marging_v;
                inner.y += cut;
                inner.height -= cut;
            }
        } 
        return inner;
    }

    ////////////// Touch interface ///////////////////
    // All fields is -1 if no touch
    struct TouchCell {
        int row = -1;
        int col = -1;
        int id = -1;
    };
    TouchCell get_touch(int x, int y) const;

    ///////////// Runtime geomentry/contents manipulation ////////////////////////////////
    void swap_geometry(const Geometry*);
    void set_cell_id(int row, int col, int id) 
    {
        initial_geom_eval(); 
        auto& c = cell(row, col); 
        if (c.id != id) {c.id = id; c.updated |= UI_Text;}
    }
    int get_cell_id(int row, int col) const {assert(!cells.empty()); return cell(row, col).id;}
    void set_cell_box(int row, int col, int box_idx) 
    {
        initial_geom_eval(); 
        auto& c = cell(row, col); 
        ++box_idx; 
        if (c.box_index != box_idx) {c.box_index = box_idx; c.updated |= UI_Box;}
    }
    int get_cell_box(int row, int col) const {assert(!cells.empty()); return cell(row, col).box_index-1;}

    // Change setup for box 'box_index'. Valid values 0 and 1
    // All affected grid cell marked for update
    void change_box(int box_index, const char* setup)
    {
        ++box_index;
        box_defs[box_index].setup(setup);
        for(auto& c: cells)
            if (c.box_index == box_index)
                c.updated |= UI_Box;
    }

    ////////////// Updates management /////////////////////////////////////////////////////
    // Mark cells to redraw. Set row_count and/or col_count to 0 to update to the end of row/column
    void invalidate(int row, int col, int how=UI_Text, int row_count=1, int col_count=1)
    {
        initial_geom_eval();

        if (!row_count) row_count = this->row_count - row;
        if (!col_count) col_count = this->col_count - col;

        for(int r=0; r<row_count; ++r)
            for(int c=0; c<col_count; ++c)
                cell(r+row, c+col).updated |= how;
    }

    bool need_update() const
    {
        for(const auto& c: cells) if (c.updated) return true;
        return false;
    }

    ///////// Draw members ////////////////////////

    // Draw subgrid (row/col by row_count/col_count cells) with shift dx/dy from its original position.
    // Keep track of dx/dy changes to clear possible tails of previous subgrid images
    // History cleared by 'update' call
    void draw_float(LCD&, int row, int col, int row_count, int col_count, int dx, int dy);

    // Prepare to draw Grid inside supplied coordinates and Draw them
    void set_coord(LCD& lcd, const Rect&);

    // Draw grid on screen
    void update(LCD&, bool with_spacers=false);

    // Draw everything
    void update_all(LCD&);

    // Setup LCD text color by box index
    void set_lcd_color(LCD& lcd, int idx)
    {
        const auto& B = box_defs[idx];
        lcd.set_bg(B.bg_color);
        lcd.set_fg(B.fg_color);
    }
};


} // namespace GridManager
