xvrxvr/EventCalendar/soft/firmware/main/activity.cpp

#include "common.h"

#include "activity.h"
#include "input_hw.h"
#include "input_hw_touch.h"
#include "input_hw_fg.h"
#include "web_gadgets.h"

static constexpr int MAX_ACTIVITIES = 4;

static const char TAG[] = "activity";

static TouchInput touch_input;
static FGInput fg_input;

static Activity* all_activities[MAX_ACTIVITIES];

static SemaphoreHandle_t activity_lock;

static QueueHandle_t pending_messages;

class L {
public:
    L() {xSemaphoreTake(activity_lock, portMAX_DELAY);}
    ~L() {xSemaphoreGive(activity_lock);}
};

Activity::Activity(uint32_t /* bitset of ActionType and ActionFlags*/ actions, uint32_t /* bitset of ActionType*/ can_be_borrowed_actions) : actions(actions), can_be_borrowed_actions(can_be_borrowed_actions)
{
    actions_queue = xQueueCreate(16, sizeof(Action));
    L lock;
    int empty_idx = -1;
    for(int i=MAX_ACTIVITIES; --i;)
    {
        auto a = all_activities[i];
        if (!a) {empty_idx = i; continue;}
        if (a->actions & actions & (AT_Fingerprint|AT_TouchBit)) {status_ok = false; locked_out |= 1<< i;}
        if (a->can_be_borrowed_actions & can_be_borrowed_actions) {status_ok = false; actions &= ~AF_Override; break;} // This is definitely error - Override will not work
    }
    if (!(actions & AF_CanFail)) status_checked = true;
    if (!(actions & AF_Override))
    {
        assert(status_ok || (actions & AF_CanFail));
    }
    assert(empty_idx != -1);
    all_activities[empty_idx] = this;
    my_index = empty_idx;
    if (!status_ok)
    {
        if (!(actions & AF_Override)) return; // This is error case - just return
        // Otherwise - lock out all conflicting
        status_ok = true;
        for(int i=0; i<MAX_ACTIVITIES; ++i)
        {
            auto a = all_activities[i];
            if (!a) continue;
            if ((locked_out >> i) & 1) a->lock_out();
        }
    }
    for(int i=0; i<MAX_ACTIVITIES; ++i)
    {
        auto a = all_activities[i];
        if (!a || a->suspended) continue;
        if (actions & a->can_be_borrowed_actions & ~a->borrowed) // borrow something
        {
            a->borrowed |= actions & a->can_be_borrowed_actions;
            a->push_spc_code(IA_Borrow, actions & a->can_be_borrowed_actions);
        }
    }
}

void Activity::add_actions(uint32_t extra) 
{
    L lock;
    actions |= extra;
}

void Activity::lock_out()
{
    if (suspended) return;
    suspended = true;
    push_spc_code(IA_Suspend);
    if (alarm_timer) xTimerStop(alarm_timer, portMAX_DELAY);
}

void Activity::unlock_out()
{
    if (!suspended) return;
    suspended = false;
    push_spc_code(IA_Resume);
    if (alarm_timer) setup_alarm_action(setup_alarm_time);
}

Activity::~Activity() 
{
    {
        L lock;
        all_activities[my_index] = NULL;
        if (status_ok) // Unlock (if any) and returns
        {
            for(int i=0; i<MAX_ACTIVITIES; ++i)
            {
                auto a = all_activities[i];
                if (!a) continue;
                // Situation when locked out Activity was removed during lock and some new was created in that place is not handled - it's almost impossible to ocure
                if ((locked_out >> i) & 1) a->unlock_out(); else
                if (actions & a->can_be_borrowed_actions) // borrow something
                {
                    a->borrowed &= ~(actions & a->can_be_borrowed_actions);
                    a->push_spc_code(IA_Return, actions & a->can_be_borrowed_actions);
                }
            }
        }
    }
    if (alarm_timer) xTimerDelete(alarm_timer, portMAX_DELAY);
    vQueueDelete(actions_queue);
}

Activity& Activity::setup_alarm_action(time_t time_to_hit)
{
    check();
    setup_alarm_time = time_to_hit;
    if (!(actions & AT_Alarm)) return *this;
    if (!alarm_timer)
    {
        alarm_timer = xTimerCreate("Activity-Alarm", hit_to_ticks(time_to_hit), 0, this, &Activity::alarm_proxy);
        xTimerStart(alarm_timer, portMAX_DELAY);
    }
    else
    {
        xTimerChangePeriod(alarm_timer, hit_to_ticks(time_to_hit), portMAX_DELAY);
    }
    return *this;
}

// Global entry - push Action in pending queue. It will be retrieved by first Activity that enabled for this type of Action
void Activity::queue_action(const Action& act)
{
    xQueueSend(pending_messages, &act, portMAX_DELAY);
}

Action Activity::get_action() //Return input action. Blocks until action will be available.
{
    Action result;
    check();

    auto actions = active_actions();
    while(xQueuePeek(pending_messages, &result, 0))
    {
        if (result.type & actions) 
        {
            xQueueReceive(pending_messages, &result, 0);
            return result;
        }
    }

    for(;;)
    {
        auto actions = active_actions();
        if (actions & AT_Fingerprint)
        {
            uint32_t col = 0;
            switch(actions & AT_Fingerprint2)
            {

                case AT_Fingerprint: col = auraLEDCode(FINGERPRINT_SENSOR_NORMAL_COLOR); break;
                case AT_Fingerprint0: col = auraLEDCode(FINGERPRINT_SENSOR_HIDDEN); break;
                case AT_Fingerprint1: col = auraLEDCode(FINGERPRINT_SENSOR_OOB_COLOR); break;
                case AT_Fingerprint2: col = custom_fg_color; break;
            }
            fg_input.cmd(col);
        }
        if (actions & AT_TouchBit) touch_input.cmd(actions & (AT_TouchBit|AT_TouchDown|AT_TouchUp|AT_TouchTrack));
        if (update_scene_req)
        {
            update_scene_req = false;
            update_scene(LCDAccess(this).access());
        }
        if (!xQueueReceive(actions_queue, &result, setup_watchdog_time && !suspended ? setup_watchdog_time : portMAX_DELAY))
        {
            result = Action{.type = AT_WatchDog};
        }
        if (result.type == AT_Internal)
        {
            switch(result.internal.code)
            {
                case IA_Suspend: on_suspend(); break;
                case IA_Resume:  update_scene_req = true; on_resume(); break;
                case IA_Borrow: on_action_borrow(ActionType(result.internal.p1)); break;
                case IA_Return: on_action_return(ActionType(result.internal.p1)); break;
            }
            continue;
        }
        return result;
    }    
}

void Activity::push_action(const Action& action)
{
    L lock;
    for(int i=0; i<MAX_ACTIVITIES; ++i)
    {
        auto a = all_activities[i];
        if (!a) continue;
        if (a->active_actions() & action.type) a->push_action_local(action);
    }
}

// void Activity::on_web_ping_echo(const char* tag) // Global entry - dispatched to all active WEB ping sources
// {
//     L lock;
//     for(int i=0; i<MAX_ACTIVITIES; ++i)
//     {
//         auto a = all_activities[i];
//         if (!a || !a->web_ping_tag || a->locked_out || strcmp(tag, a->web_ping_tag)) continue;
//         a->web_ping_counter = 0;        
//     }
// }

void Activity::send_web_ping() // Internal function - called by WEB ping thread in this module.
{
    L lock;
    for(int i=0; i<MAX_ACTIVITIES; ++i)
    {
        auto a = all_activities[i];
        if (!a || !a->web_ping_tag || a->locked_out) continue;
        send_web_ping_to_ws(a->web_ping_tag);
        // ++a->web_ping_counter;
        // if (a->web_ping_counter > SC_WEBPing_Pings)
        // {
        //     a->push_action_local({.type = AT_WEBEvent, .web = {.event = WE_Logout, .logout_tag = a->web_ping_tag}});
        //     a->web_ping_counter = 0;
        // }
    }
}

static void web_ping_task(void*)
{
    for(;;)
    {
        Activity::send_web_ping();
        vTaskDelay(ms2ticks(SC_WEBPing_Time));
    }
}

void Activity::start()
{
    activity_lock = xSemaphoreCreateMutex();
    pending_messages = xQueueCreate(SC_ActivityQueueLength, sizeof(Action));
    touch_input.start();
    fg_input.start();
    xTaskCreate(web_ping_task, "WEB-Ping", TSS_WEBPing, NULL, TP_WEBPing, NULL);
}

Activity::LCDAccess::LCDAccess(Activity* a)
{
//    assert(a || !touch_input.is_started());
    touch_input.suspend();
}

Activity::LCDAccess::~LCDAccess()
{
    touch_input.resume();
}

Activity::FPAccess::FPAccess(Activity* a)
{
//    assert(a || !fg_input.is_started());
    fg_input.suspend();
}

Activity::FPAccess::~FPAccess()
{
    fg_input.resume();
}

void InputProxy::push_action(const Action& action)
{
    passivate_pending = true;
    Activity::push_action(action);
}
