xvrxvr/EventCalendar/soft/firmware/main/web_ajax_classes.h

#pragma once

#include "web_gadgets.h"

#define G(id, args) \
class AJAXDecoder_##id : public AnsGet { \
    V##args \
public: \
    AJAXDecoder_##id(httpd_req_t *req) : AnsGet(req) C##args {buf_reset();} \
    void run(); \
};

#define P(id, args) \
class AJAXDecoder_##id : public AnsPost { \
    V##args \
public: \
    AJAXDecoder_##id(httpd_req_t *req) : AnsPost(req) C##args {buf_reset();} \
    void run(); \
};

#define S(id) \
class AJAXDecoder_##id : public AnsStream { \
public: \
    AJAXDecoder_##id(httpd_req_t *req) : AnsStream(req) {} \
    virtual size_t consume_stream(uint8_t* buffer, size_t size, bool eof) override; \
};


#define VARG(tp, id) Arg##tp arg_##id;
#define CARG(tp, id) , arg_##id(decode_##tp(#id))

#include "web_actions.inc"
